Circuit-Digest/ESP32-AI-SmartGlass/Firmware/Smartglass4/camera_index.h

#define index_ov2640_html_gz_len 3168
const uint8_t index_ov2640_html_gz[] = {
0x1F, 0x8B, 0x08, 0x00, 0x32, 0xED, 0x11, 0x67, 0x02, 0xFF, 0xED, 0x5C, 0xFD, 0x72, 0xDB, 0x36, 0x12, 0xFF, 0x3F, 0x4F, 0x81, 0xD0, 0x6D, 0x24, 0xB5, 0xA2, 0xBE, 0x2C, 0xCB, 0x8E, 0x2C, 0xA9, 0x97, 0xA6, 0x4E, 0x9C, 0xB9, 0x64, 0xDA, 0xC6, 0xED, 0x4D, 0x66, 0x32, 0x99, 0x0B, 0x44, 0x42, 0x12, 0x63, 0x8A, 0x60, 0x41, 0x48, 0x96, 0x93, 0xF1, 0x73, 0xDC, 0x03, 0xDD, 0x8B, 0xDD, 0x02, 0x24, 0x25, 0x92, 0x02, 0xF8, 0x21, 0xF5, 0xAE, 0x77, 0xD3, 0xB3, 0x1B, 0x8B, 0x12, 0x17, 0x8B, 0xC5, 0x7E, 0xFC, 0x76, 0x17, 0x84, 0x3A, 0x7A, 0x6C, 0x53, 0x8B, 0xDF, 0xFB, 0x04, 0x2D, 0xF8, 0xD2, 0x9D, 0x3C, 0x1A, 0x85, 0x2F, 0x08, 0x7E, 0x46, 0x0B, 0x82, 0xED, 0xF0, 0x52, 0xBE, 0x5D, 0x12, 0x8E, 0x91, 0xB5, 0xC0, 0x2C, 0x20, 0x7C, 0x6C, 0xAC, 0xF8, 0xCC, 0xBC, 0x30, 0xB2, 0xB7, 0x3D, 0xBC, 0x24, 0x63, 0x63, 0xED, 0x90, 0x3B, 0x9F, 0x32, 0x6E, 0x20, 0x8B, 0x7A, 0x9C, 0x78, 0x40, 0x7E, 0xE7, 0xD8, 0x7C, 0x31, 0xB6, 0xC9, 0xDA, 0xB1, 0x88, 0x29, 0xDF, 0x34, 0x1D, 0xCF, 0xE1, 0x0E, 0x76, 0xCD, 0xC0, 0xC2, 0x2E, 0x19, 0x77, 0x93, 0xBC, 0xB8, 0xC3, 0x5D, 0x32, 0xB9, 0xBA, 0xF9, 0xE9, 0xB4, 0x87, 0x9E, 0xBD, 0x42, 0x37, 0x4B, 0xCC, 0x38, 0x7A, 0xE9, 0xE2, 0x20, 0x18, 0xB5, 0xC3, 0x7B, 0x3B, 0xDA, 0x80, 0xDF, 0x27, 0xDF, 0x8B, 0x9F, 0x29, 0xB5, 0xEF, 0xD1, 0x97, 0xD4, 0x47, 0xE2, 0x67, 0x06, 0xC2, 0x98, 0x33, 0xBC, 0x74, 0xDC, 0xFB, 0x21, 0x7A, 0xC6, 0x60, 0xEE, 0x26, 0xBA, 0x26, 0xEE, 0x9A, 0x70, 0xC7, 0xC2, 0x4D, 0x14, 0x60, 0x2F, 0x30, 0x03, 0xC2, 0x9C, 0xD9, 0xE5, 0xDE, 0xD0, 0x29, 0xB6, 0x6E, 0xE7, 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
  0x0F, 0x0E, 0xB3, 0xA7, 0x0A, 0x4A, 0x02, 0xC1, 0xE0, 0xDD, 0xCB, 0x9E, 0x9A, 0xB0, 0x10, 0xB1, 0xAF, 0x1D, 0xB0, 0x83, 0x12, 0x79, 0x8A, 0xA0, 0xF1, 0x4C,
  0x42, 0x74, 0xA9, 0xBD, 0xB0, 0x54, 0x45, 0xEA, 0x4B, 0x71, 0x6B, 0x93, 0xA6, 0xFE, 0xB9, 0xC1, 0x22, 0x98, 0x04, 0x4E, 0x26, 0x79, 0xD3, 0xC8, 0xC9, 0xA4,
  0xD3, 0xEA, 0x74, 0x73, 0x73, 0x29, 0x29, 0x97, 0x89, 0xA9, 0xA4, 0x24, 0x98, 0x84, 0x81, 0x26, 0x5F, 0x17, 0xA7, 0x33, 0xE7, 0x9A, 0xB8, 0x12, 0x45, 0x24,
  0xC8, 0xED, 0x9E, 0x74, 0xC7, 0x0A, 0xD8, 0x0C, 0x18, 0x0A, 0xAE, 0x65, 0x81, 0x36, 0x8E, 0xAE, 0xAD, 0x8F, 0xDA, 0x99, 0x16, 0xCA, 0xD0, 0x1D, 0x80, 0x35,
  0x18, 0x43, 0x8B, 0x8C, 0x33, 0x22, 0xF7, 0x98, 0x4C, 0x8C, 0xA5, 0xE5, 0xE7, 0xC8, 0xDB, 0x68, 0xE1, 0xBF, 0xAC, 0x1E, 0xA9, 0x7B, 0xFD, 0x8A, 0x35, 0x90,
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
};
